harrypm/DomesdayDuplicator/assets/images/FX3.png

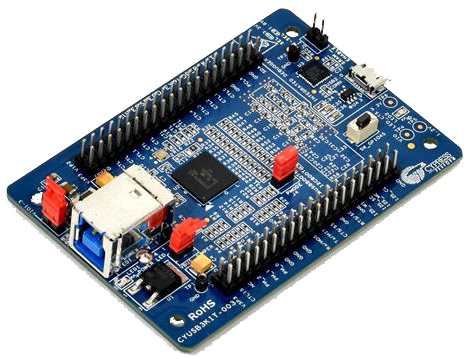
assets/images/FX3.png
